WilsonGuo23/Turntable-Arcade-Stick/V2/Turntable Right Panel Test.SLDPRT

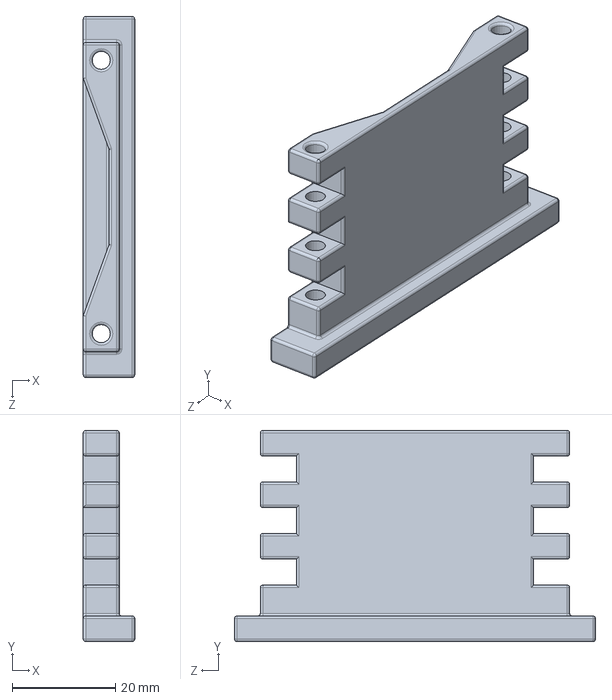
[picture p15: CAD file, 2026-03-01]
V2/Turntable Right Panel Test.SLDPRT
10.0 x 41.0 x 70.0 mm
