WilsonGuo23/Turntable-Arcade-Stick/V2/Button Panel Classic.SLDPRT

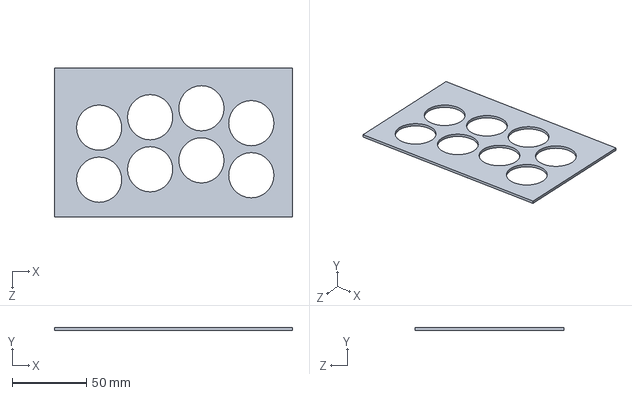
[picture p16: CAD file, 2026-03-01]
V2/Button Panel Classic.SLDPRT
160.0 x 2.00 x 100.0 mm
