WilsonGuo23/Turntable-Arcade-Stick/V1/Turntable Stick Assembly.SLDASM

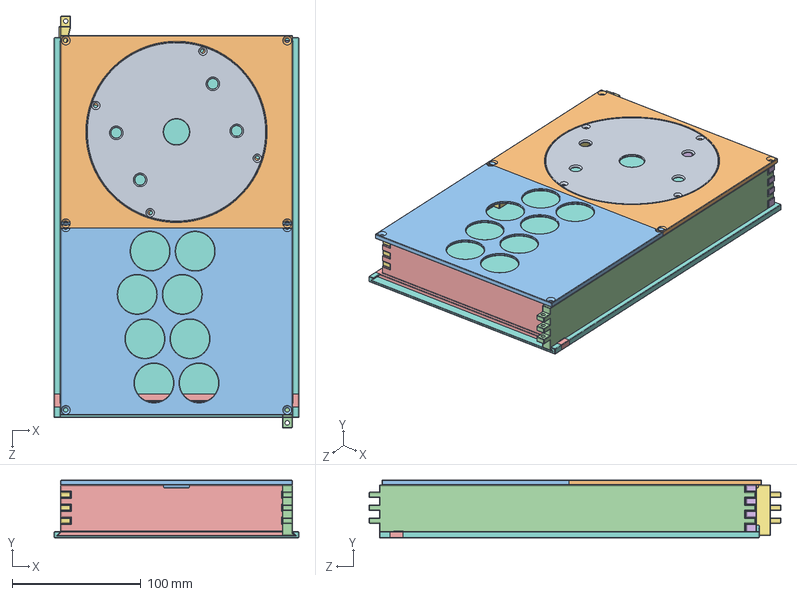
[picture p17: CAD file, 2026-03-01, an earlier design]
V1/Turntable Stick Assembly.SLDASM
190.0 x 45.0 x 320.0 mm
Quick Remove Bottom Panel
Turntable Front Panel
Turntable Left Panel
Turntable Right Panel
Turntable Back Panel
Wilson's Preferred Button Layout Panel
Turntable Movement Panel
Turntable Panel For Joystick
