WilsonGuo23/Turntable-Arcade-Stick/V1/Wilson's Preferred Button Layout Panel.SLDPRT

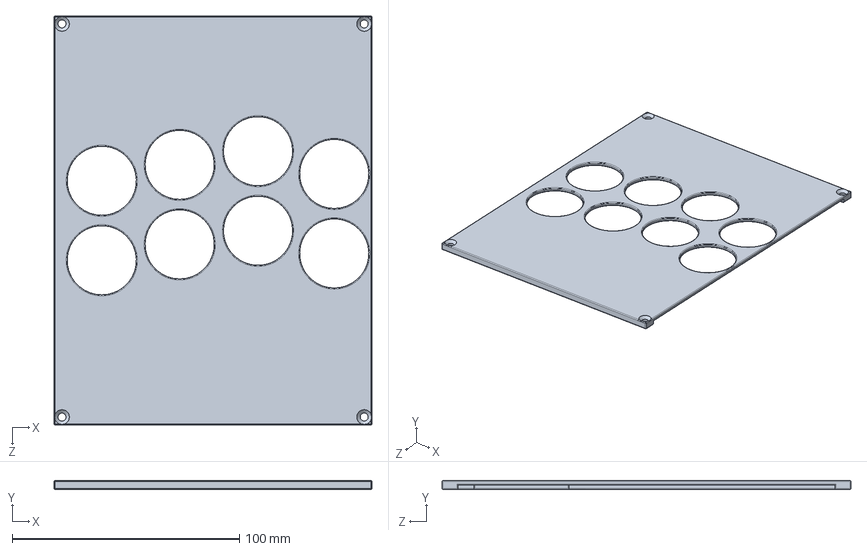
[picture p18: CAD file, 2026-03-01, an earlier design]
V1/Wilson's Preferred Button Layout Panel.SLDPRT
139.9 x 4.00 x 180.0 mm
